PolygonHJ/xihe/resources/simulations/BAT_OK Signal.asc

B2: bv; V=if(V(CAP)>2.5,V(CAP),0)
C1: cap; 470m; Rser=13m
D1: diode
M1: nmos; BSB012N03LX3
M2: pmos; FDS6575
R1: res; R=5.3/0.8
R2: res; 1Meg
R5: res; R=V(CAP)/1u
R6: res; 1Meg
R7: res; 1
R8: res; 1Meg
RLOAD: res; R=V(CAP)/100m
S1: sw; MYSW2
V1: voltage; PULSE(0 5.3 10 1p 1p 30 60)
V2: voltage; 3.3
Named nets: 0, CAP, OUT, CHG, BAT_OK, STOR, 3V3
.tran 0 100 0 startup
.model MYSW2 SW(Ron=1 Roff=10Meg Vt=0.1 Vh=0)
CAPACITOR CHARGING
BATTERY OKAY SIGNAL & OUTPUT
OUTPUT SIGNAL
PFET on CAP shows current draw.
PFET on 3V3 shows the output is kept as a 3V3 output
